rbckman/tarina/3d/tarina2.png

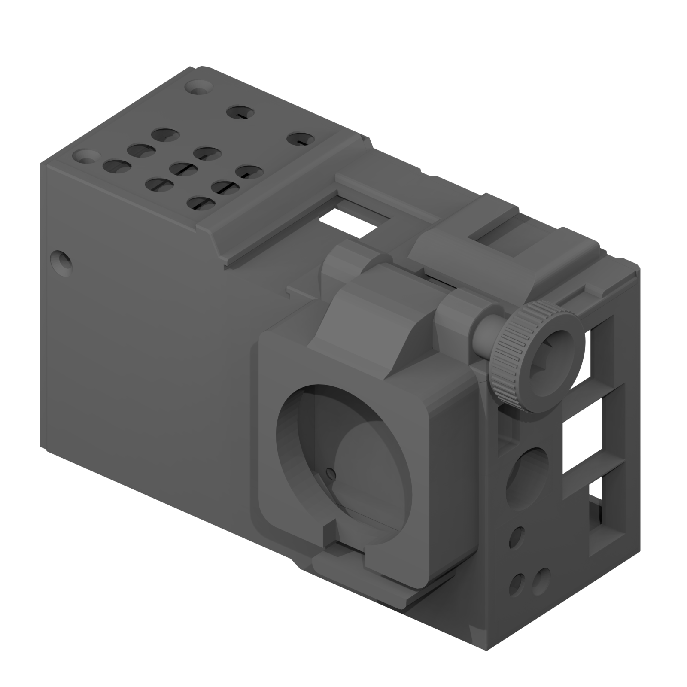
3d/tarina2.png
