rbckman/tarina/3d/tarina3.png

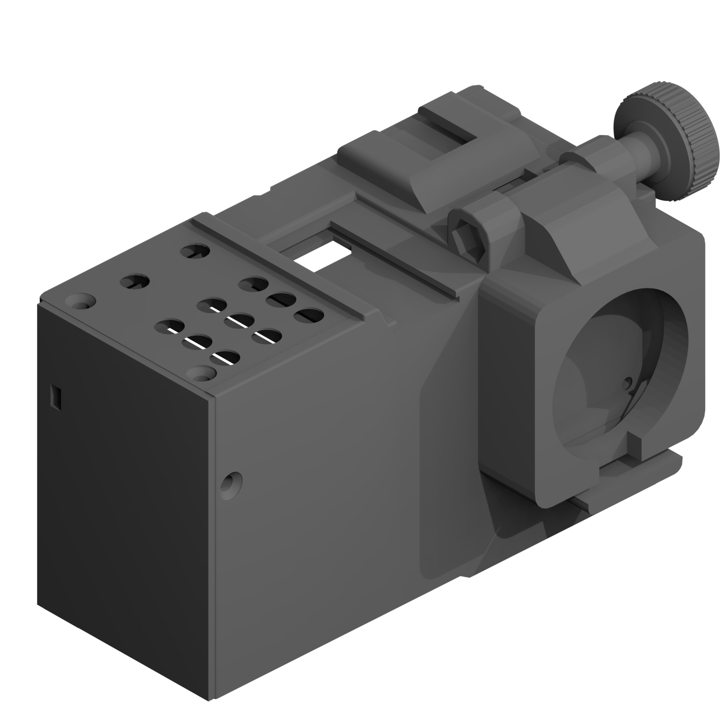
3d/tarina3.png
