rbckman/tarina/3d/tarina4.png

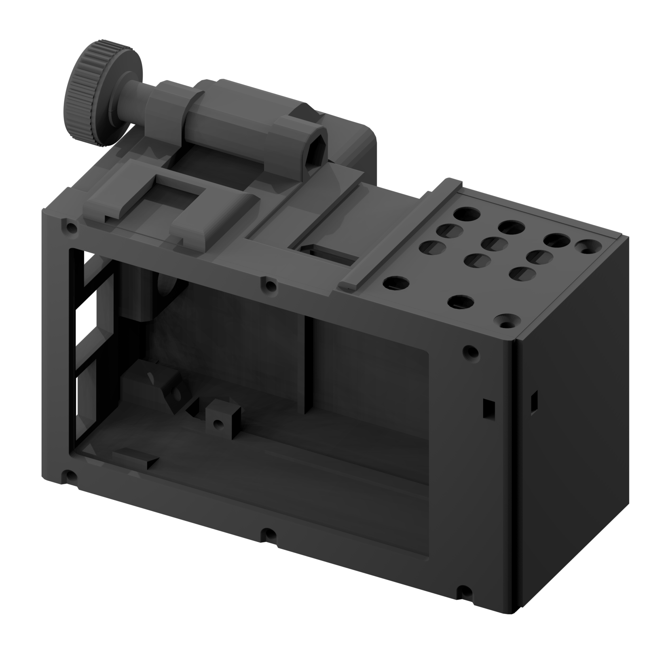
3d/tarina4.png
