rbckman/tarina/3d/tarina-body.png

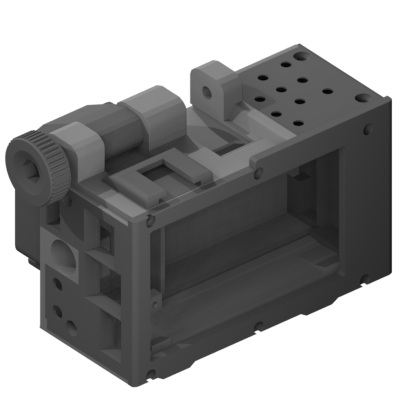
3d/tarina-body.png
