rbckman/tarina/3d/tarina-button-plate-bottom.png

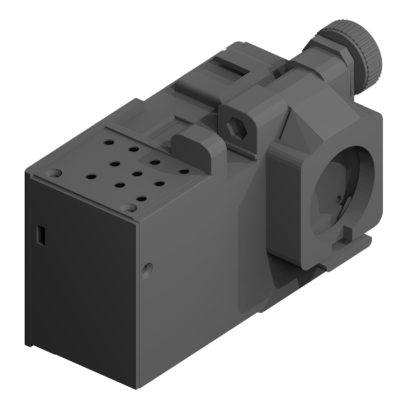
3d/tarina-button-plate-bottom.png
