rbckman/tarina/3d/tarina-button-plate-upper.png

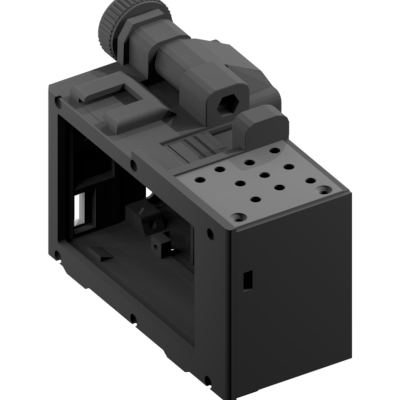
3d/tarina-button-plate-upper.png
