rbckman/tarina/3d/tarina-hdmi-cap.png

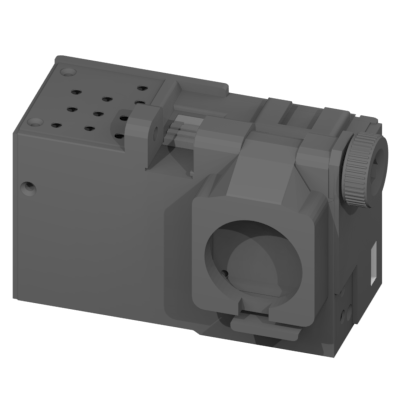
3d/tarina-hdmi-cap.png
