rbckman/tarina/3d/tarina-left-side-cap.png

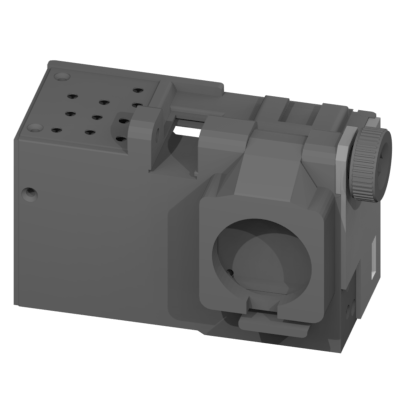
3d/tarina-left-side-cap.png
