rbckman/tarina/3d/tarina-left-side.png

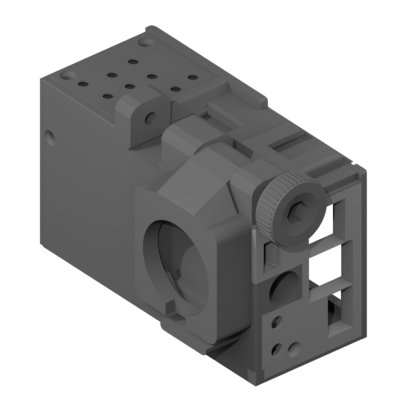
3d/tarina-left-side.png
