rbckman/tarina/3d/tarina-picamera-hq-body-lid.png

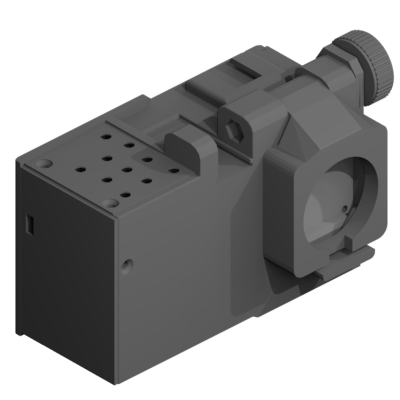
3d/tarina-picamera-hq-body-lid.png
