rbckman/tarina/3d/tarina-picamera-hq-body.png

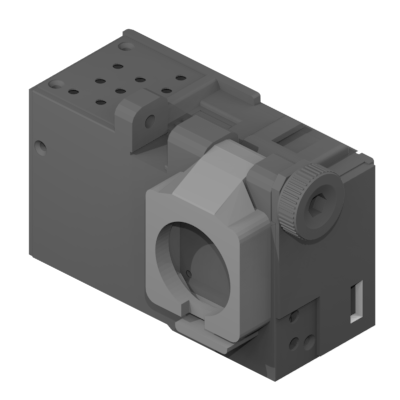
3d/tarina-picamera-hq-body.png
