rbckman/tarina/3d/tarina-picamera-screwhandle.png

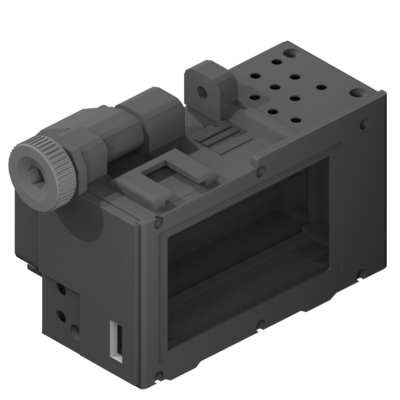
3d/tarina-picamera-screwhandle.png
