rbckman/tarina/3d/tarina-right-side.png

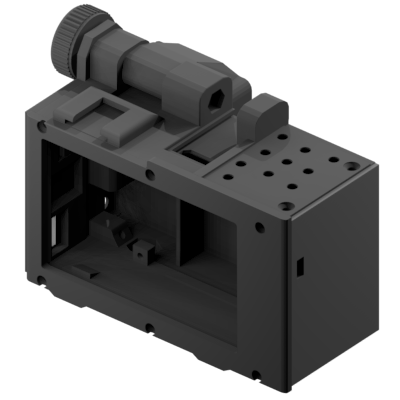
3d/tarina-right-side.png
