rbckman/tarina/3d/tarina-screen-lid-hyperpixel.png

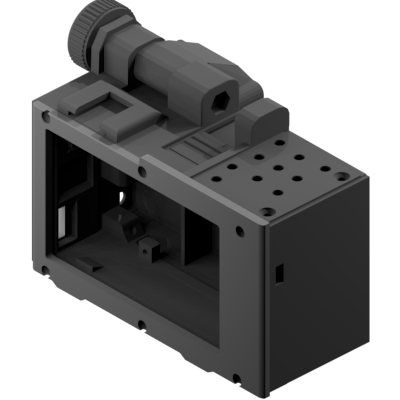
3d/tarina-screen-lid-hyperpixel.png
