rbckman/tarina/3d/tarina-screen-lid-ugeek.png

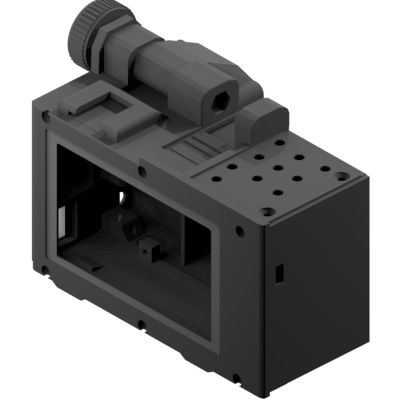
3d/tarina-screen-lid-ugeek.png
