rbckman/tarina/3d/tarina-viewfinder-hyperpixel.png

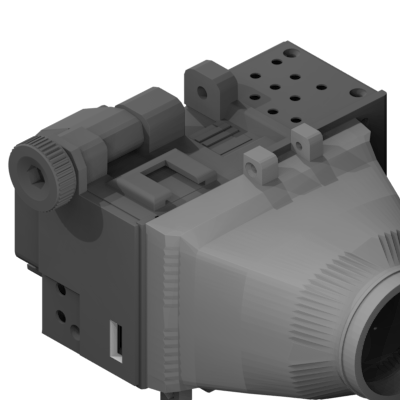
3d/tarina-viewfinder-hyperpixel.png
