rbckman/tarina/3d/tarina.png

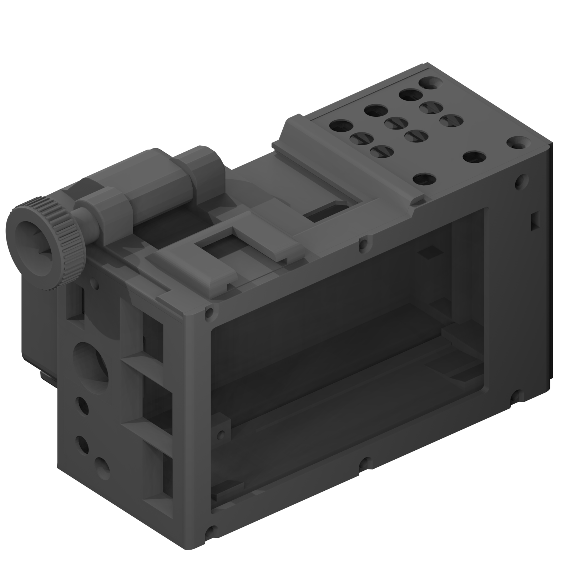
3d/tarina.png
