rbckman/tarina/docs/adafruit_powerboost1000c.png

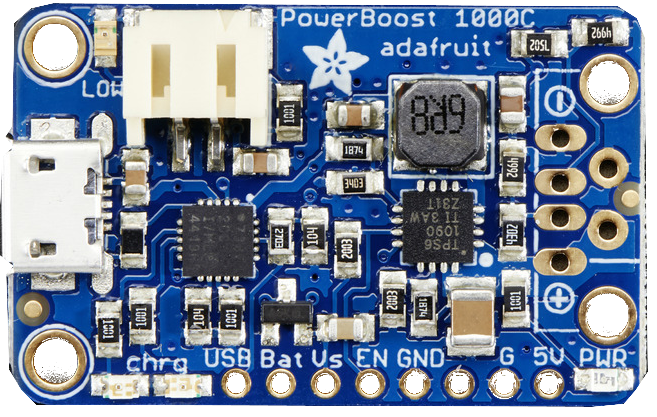
docs/adafruit_powerboost1000c.png
