rbckman/tarina/docs/hdd-cable.jpeg

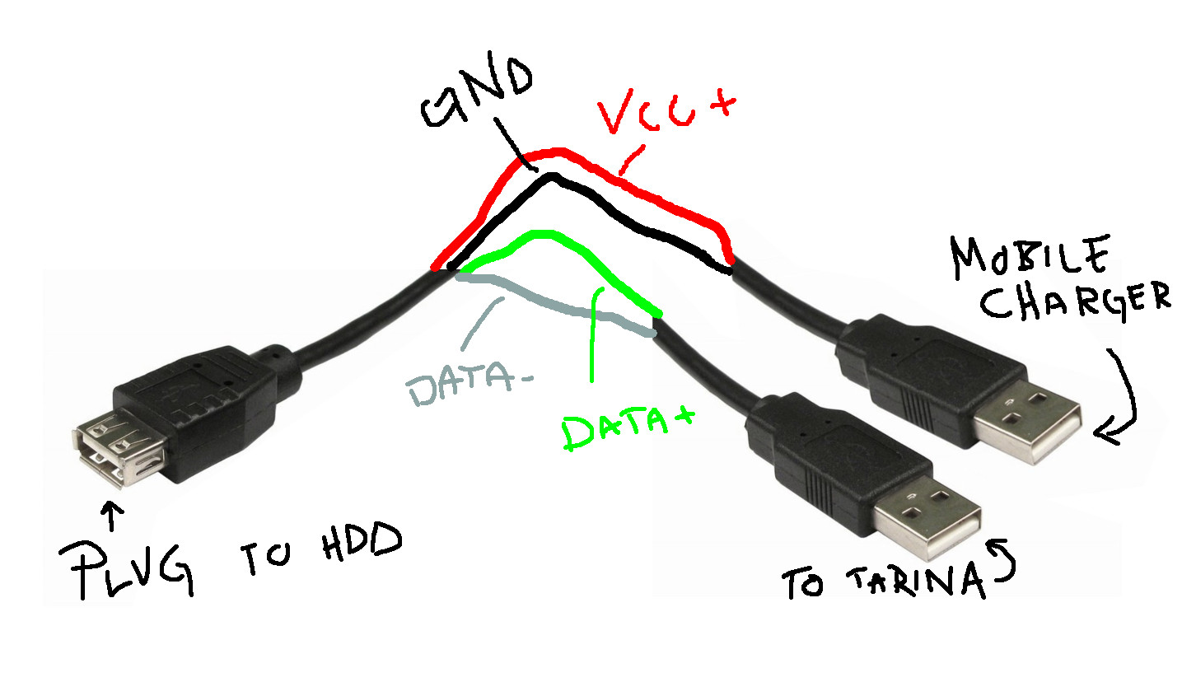
docs/hdd-cable.jpeg
