rbckman/tarina/docs/mic.png

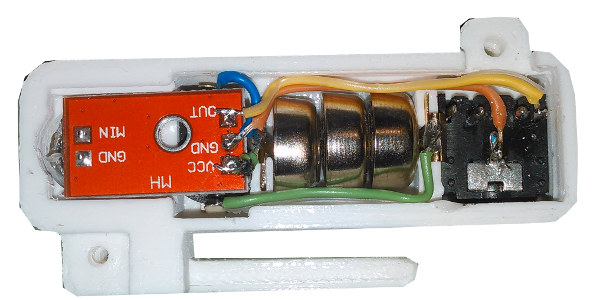
docs/mic.png
