rbckman/tarina/docs/Raspberry-Pi-3-Back.png

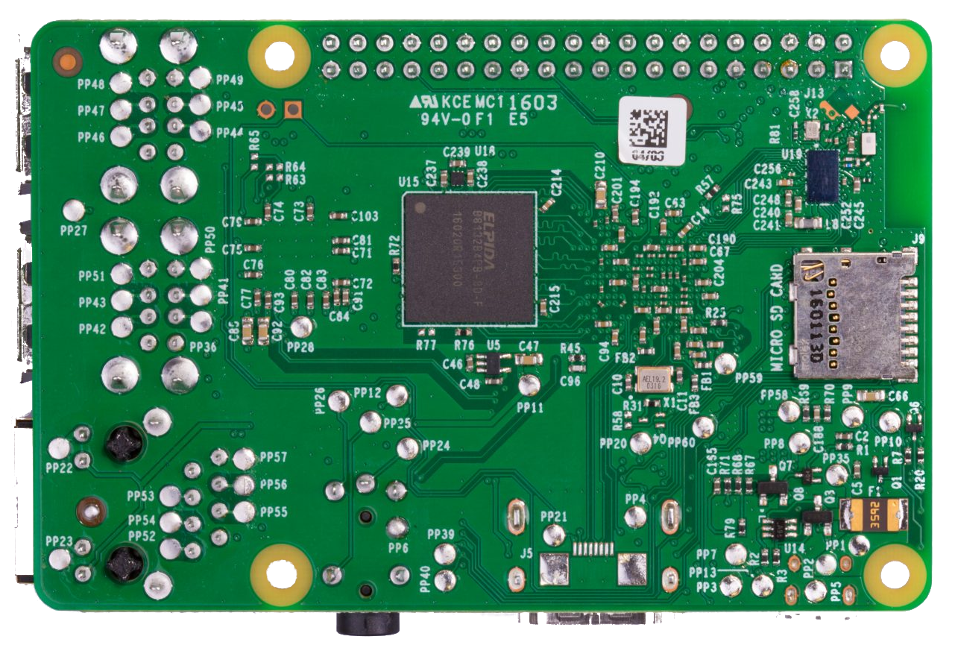
docs/Raspberry-Pi-3-Back.png
