rbckman/tarina/docs/soundcard.png

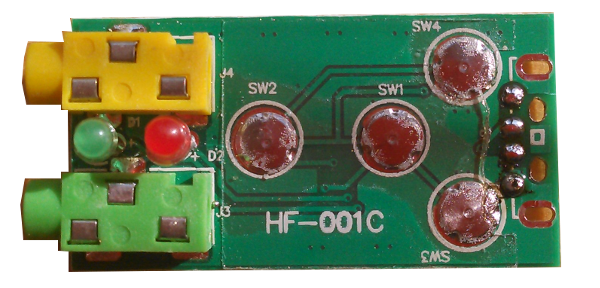
docs/soundcard.png
