rbckman/tarina/docs/tarina-and-leon.jpg

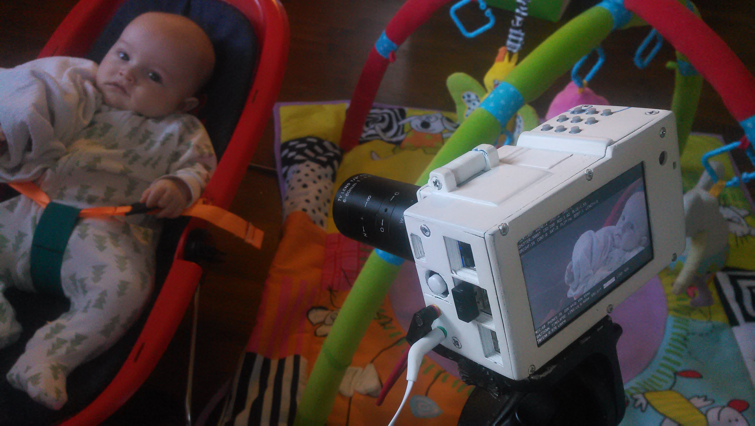
docs/tarina-and-leon.jpg
