rbckman/tarina/docs/tarina-mob.jpg

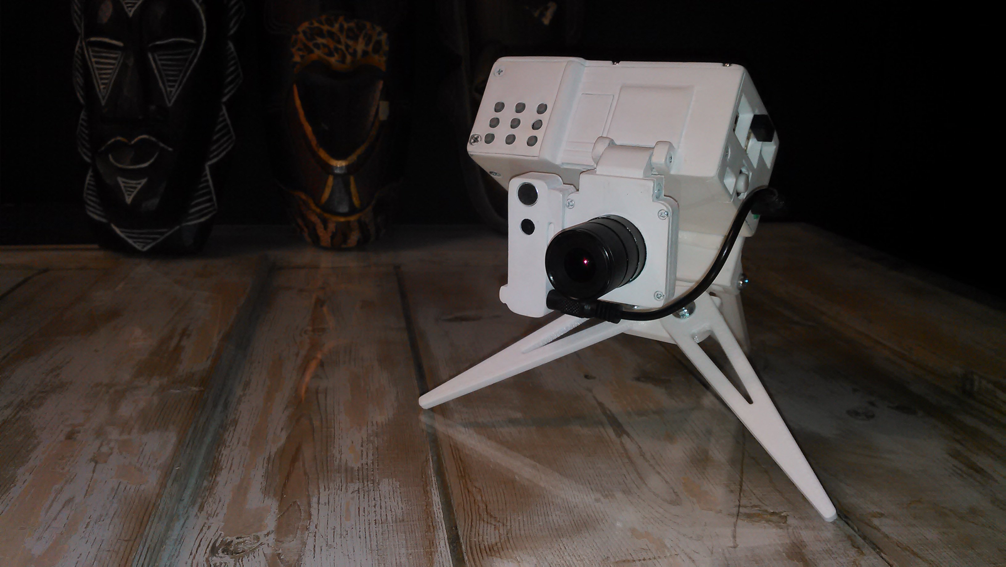
docs/tarina-mob.jpg
