rbckman/tarina/extras/buttons.png

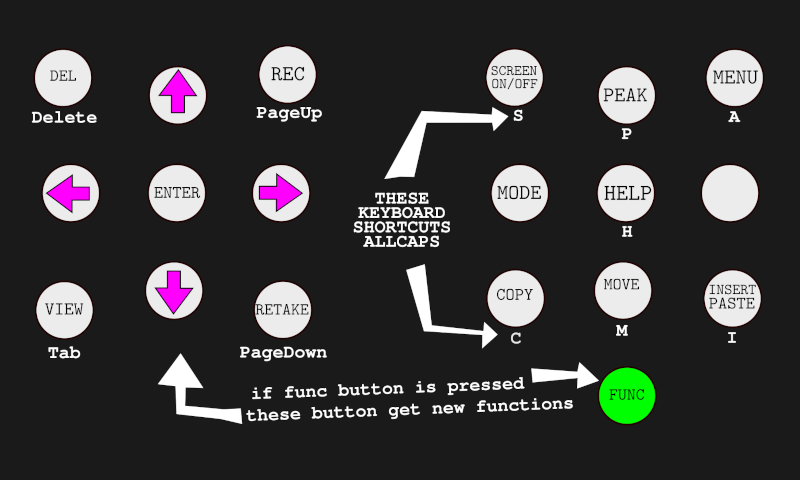
extras/buttons.png
