rbckman/tarina/3d/tarina-right-side.stl

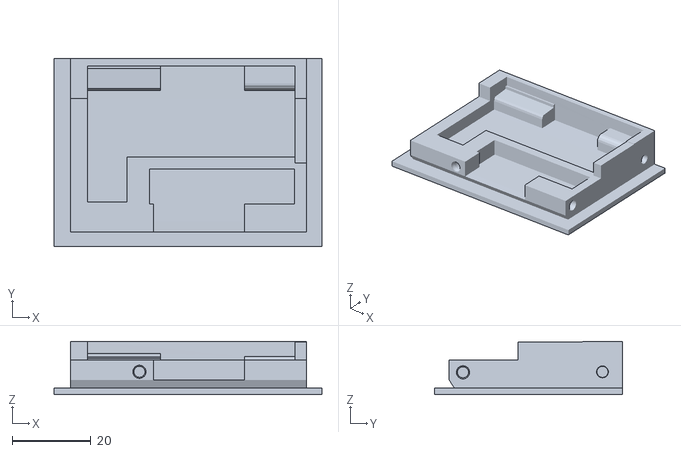
[picture p43: CAD file, 2023-09-10]
3d/tarina-right-side.stl
67.9 x 47.6 x 13.5
