rbckman/tarina/3d/tarina-screen-lid-ugeek.stl

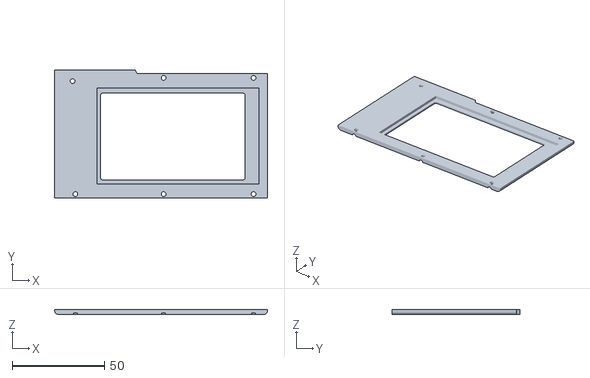
[picture p44: CAD file, 2023-09-02]
3d/tarina-screen-lid-ugeek.stl
115.7 x 69.6 x 2.70
