rbckman/tarina/3d/tarina-picamera-hq-body-lid.stl

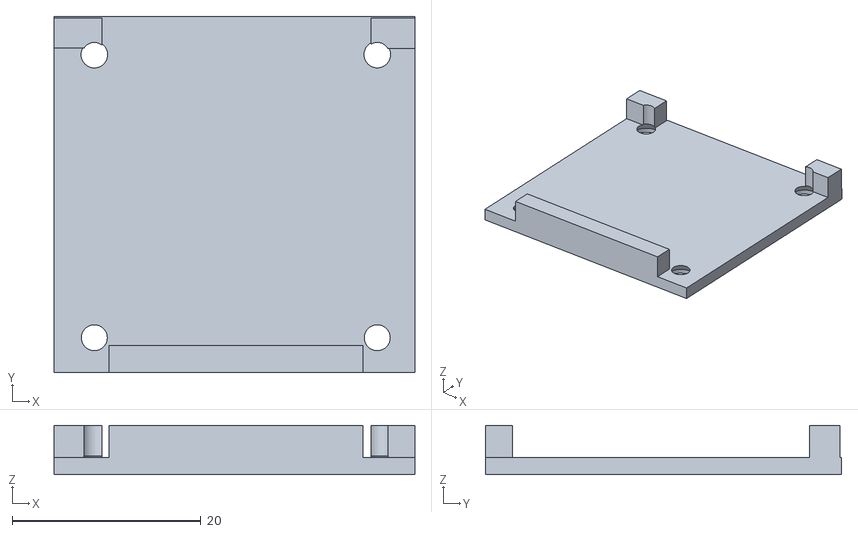
[picture p45: CAD file, 2023-09-02]
3d/tarina-picamera-hq-body-lid.stl
38.2 x 37.7 x 5.24
