rbckman/tarina/3d/viewfinder-clip-bridge3.stl

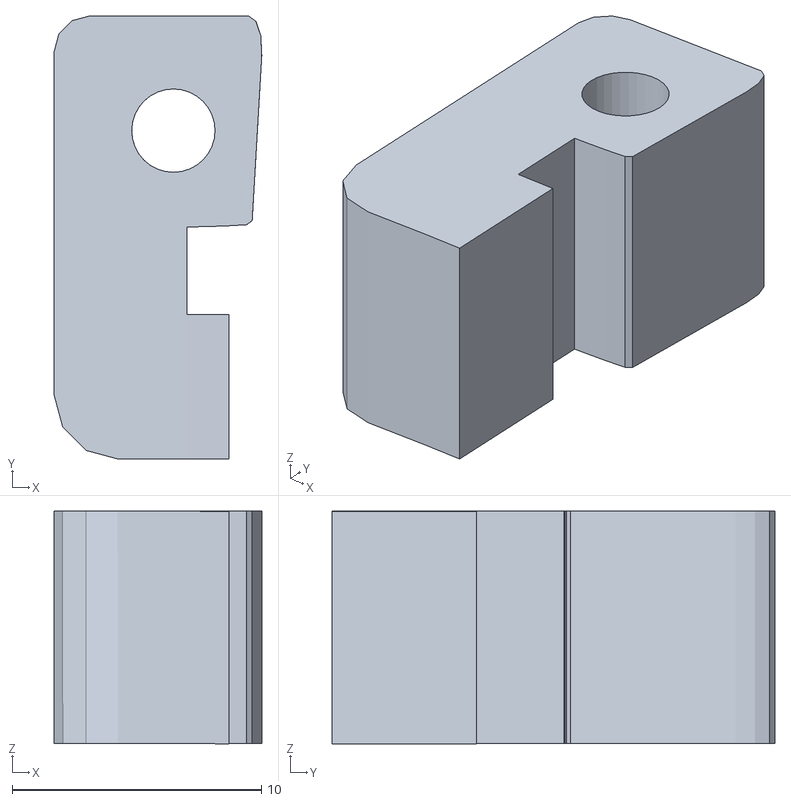
[picture p46: CAD file, 2023-08-19]
3d/viewfinder-clip-bridge3.stl
8.32 x 17.8 x 9.33
