rbckman/tarina/3d/tarina-modifyer-body-logo.stl

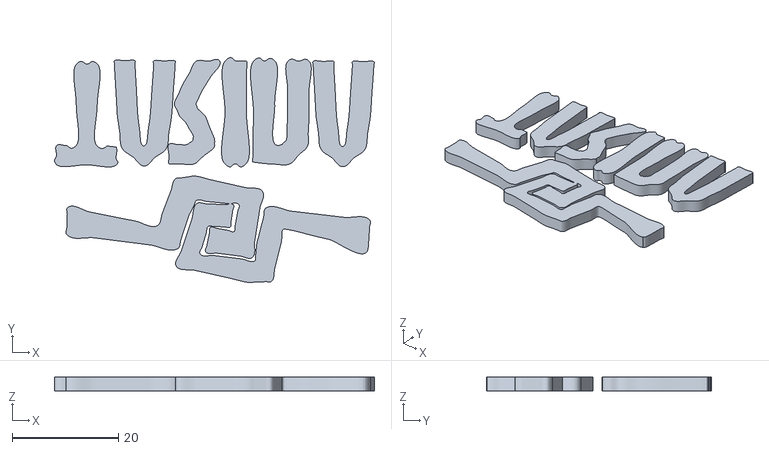
[picture p47: CAD file, 2023-08-19]
3d/tarina-modifyer-body-logo.stl
60.2 x 42.3 x 2.57
