rbckman/tarina/3d/tarina-modifyer-button-icons.stl

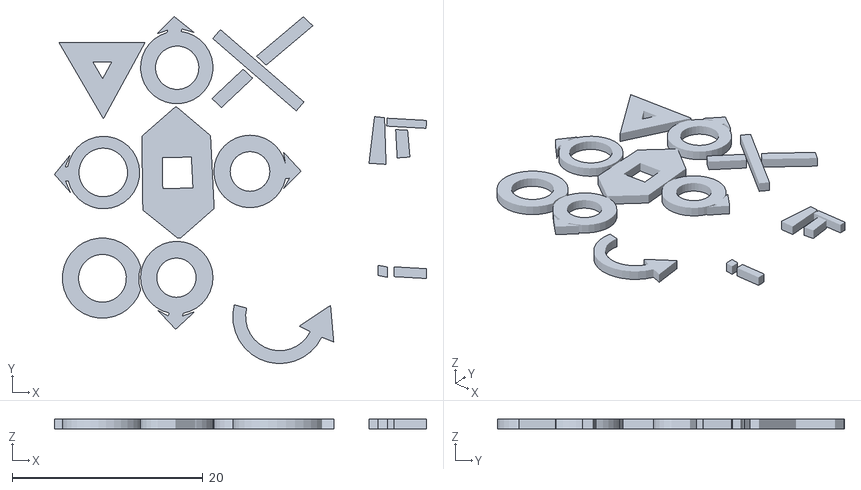
[picture p48: CAD file, 2023-08-19]
3d/tarina-modifyer-button-icons.stl
39.0 x 36.4 x 1.10
