rbckman/tarina/3d/viewfinder-clip-bridge2.stl

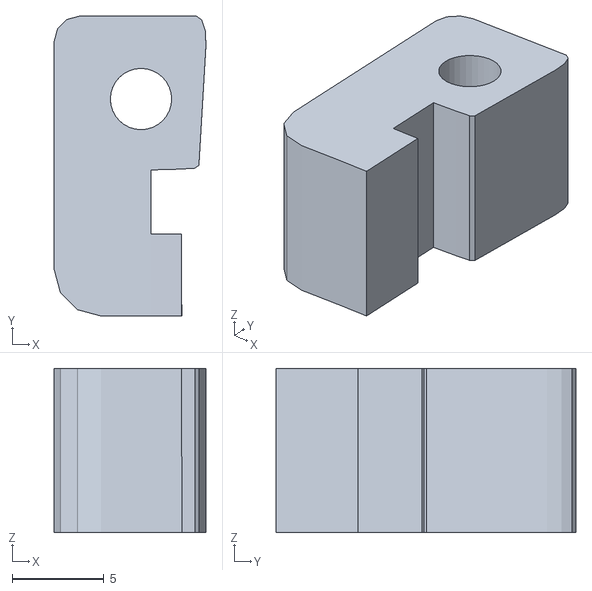
[picture p49: CAD file, 2023-08-19]
3d/viewfinder-clip-bridge2.stl
8.29 x 16.4 x 8.96
