rbckman/tarina/3d/tarina-viewfinder-hyperpixel.stl

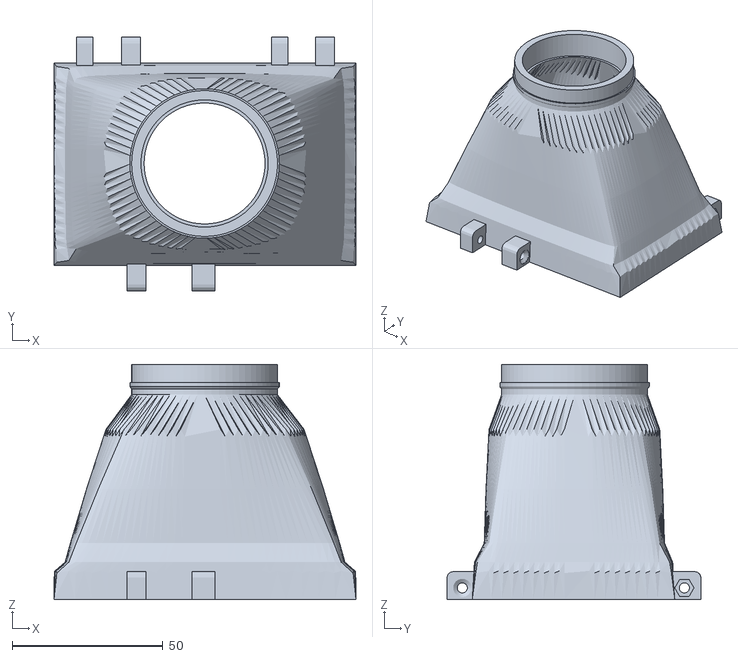
[picture p50: CAD file, 2023-08-19]
3d/tarina-viewfinder-hyperpixel.stl
100.2 x 84.3 x 78.0
