rbckman/tarina/3d/tarina-viewfinder-eyepiece.stl

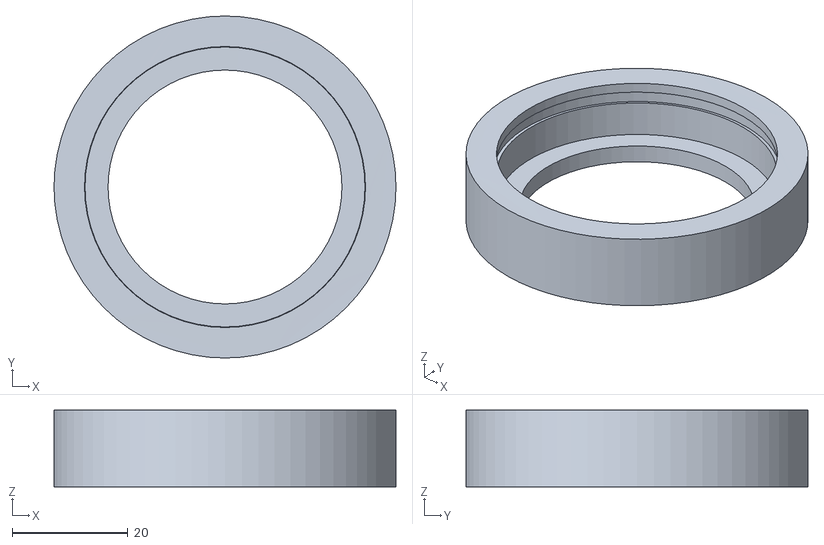
[picture p51: CAD file, 2023-08-19]
3d/tarina-viewfinder-eyepiece.stl
59.1 x 59.1 x 13.3
