rbckman/tarina/3d/viewfinder-clip-bridge.stl

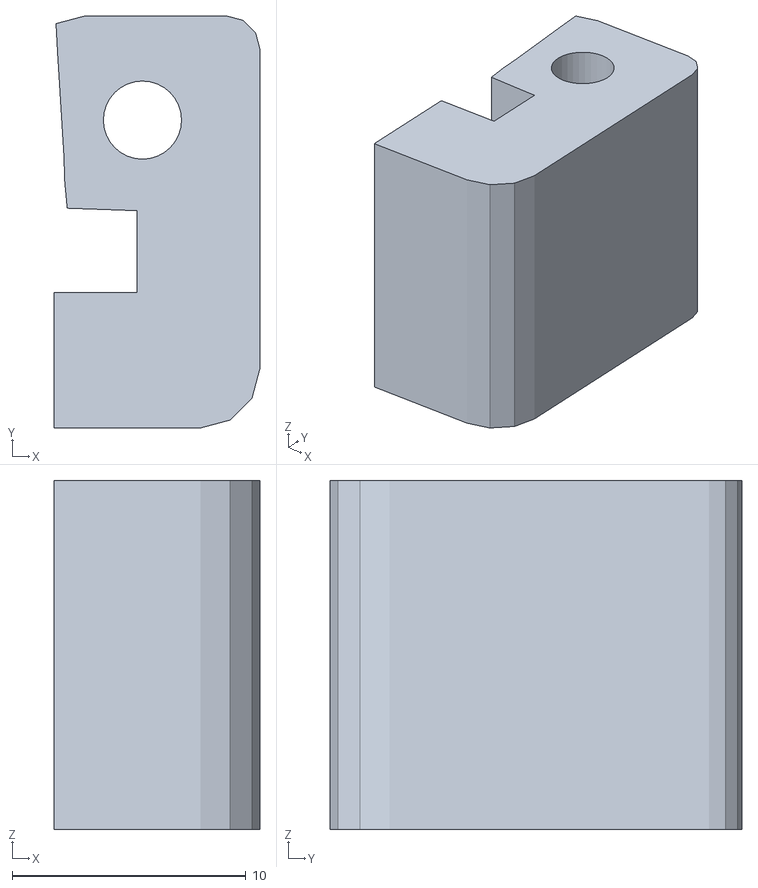
[picture p52: CAD file, 2023-08-19]
3d/viewfinder-clip-bridge.stl
8.80 x 17.6 x 14.9
