rbckman/tarina/3d/tarina-picamera-body.stl

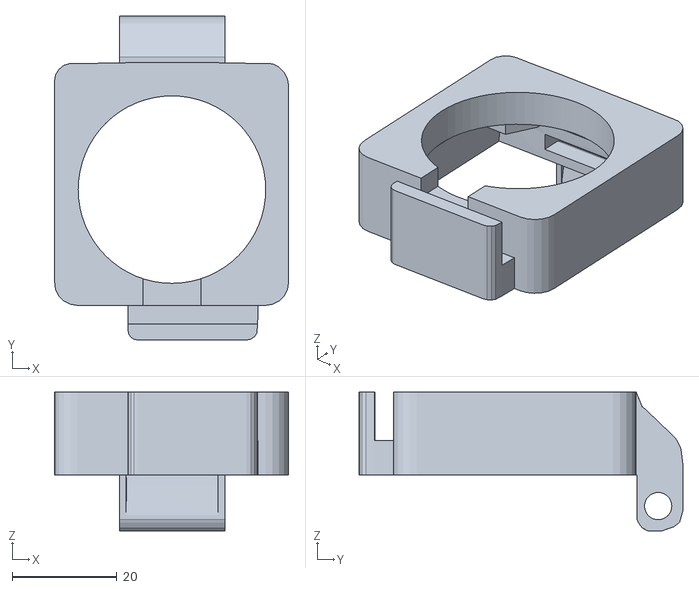
[picture p53: CAD file, 2022-04-14]
3d/tarina-picamera-body.stl
44.7 x 61.9 x 26.5
