rbckman/tarina/3d/tarina-picamera-body-lid.stl

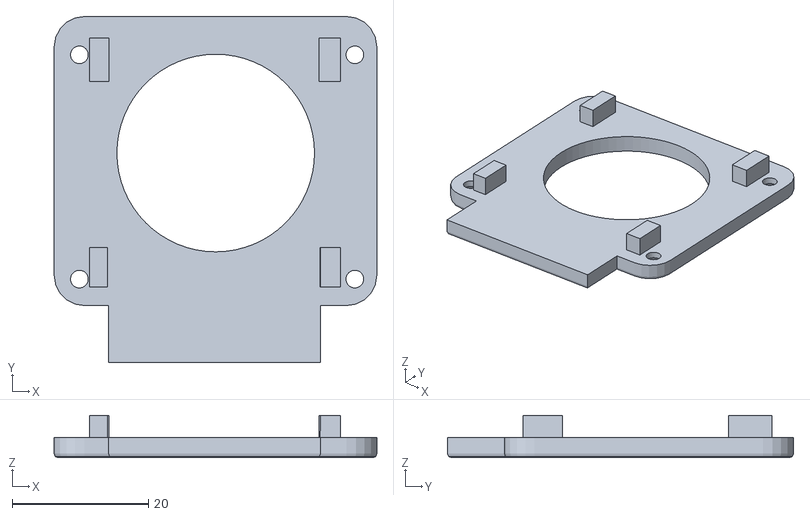
[picture p54: CAD file, 2022-01-14]
3d/tarina-picamera-body-lid.stl
47.4 x 50.8 x 6.22
