rbckman/tarina/3d/tarina-picamera-bridge.stl

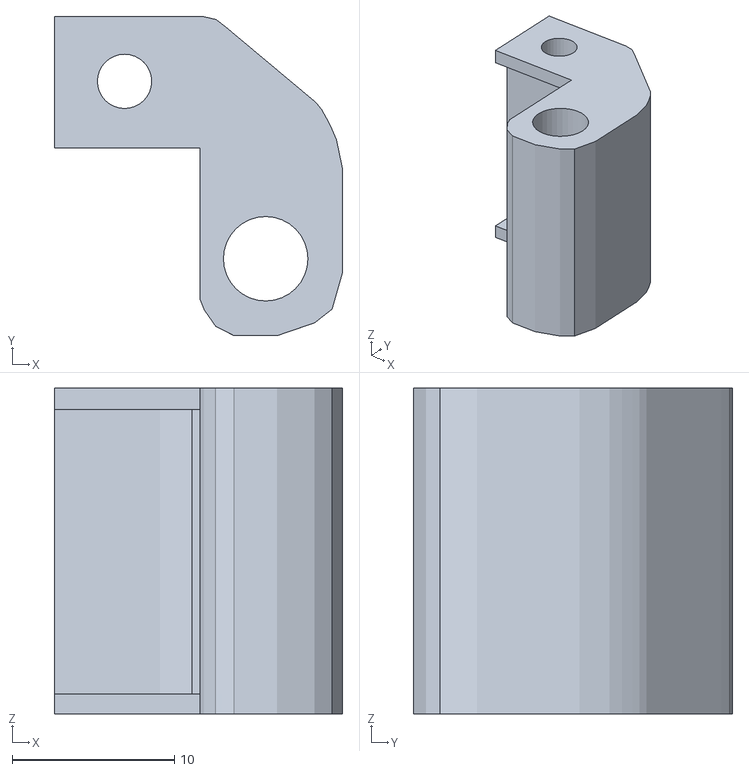
[picture p55: CAD file, 2022-01-14]
3d/tarina-picamera-bridge.stl
17.8 x 19.7 x 20.1
