rbckman/tarina/3d/tarina-screen-lid.stl

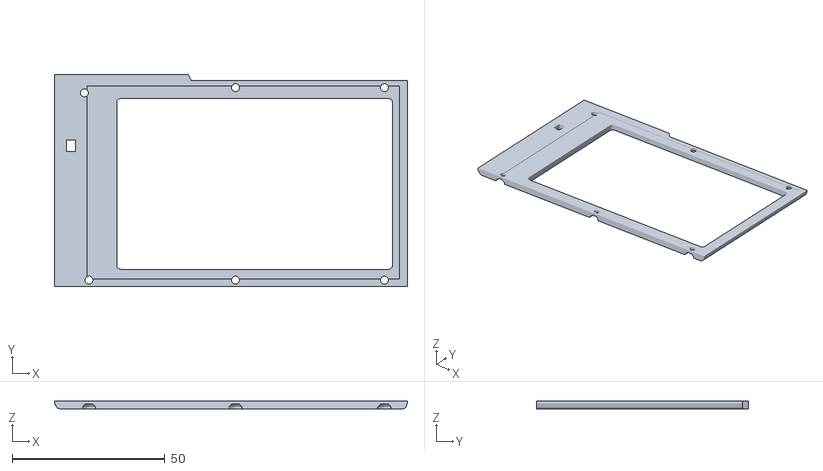
[picture p56: CAD file, 2021-04-11]
3d/tarina-screen-lid.stl
115.7 x 69.6 x 2.70
