rbckman/tarina/3d/tarina-viewfinder.stl

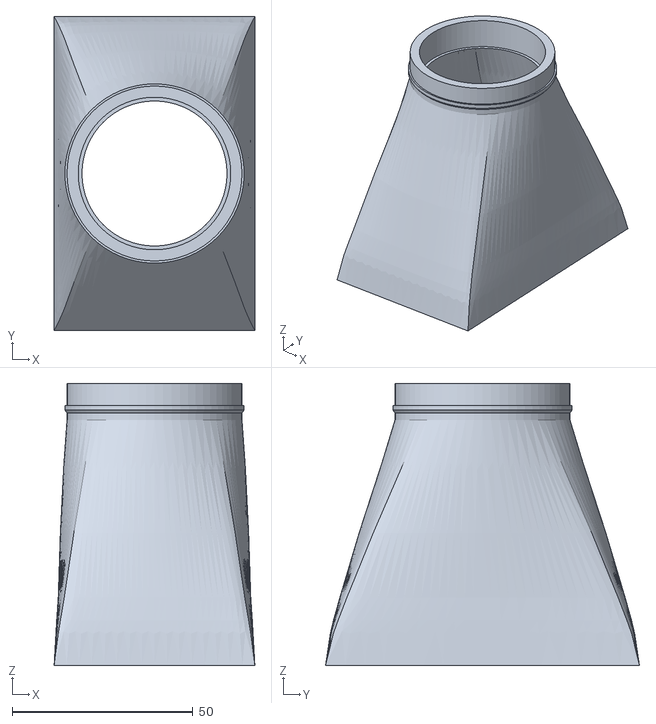
[picture p57: CAD file, 2020-01-06]
3d/tarina-viewfinder.stl
55.6 x 86.9 x 78.0
