rbckman/tarina/3d/tarina-plate.stl

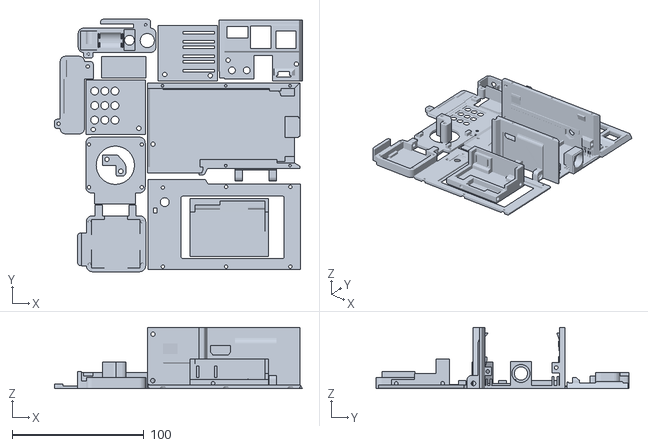
[picture p58: CAD file, 2019-12-02]
3d/tarina-plate.stl
188.3 x 191.7 x 46.5
