rbckman/tarina/docs/tarina-build-06.jpg

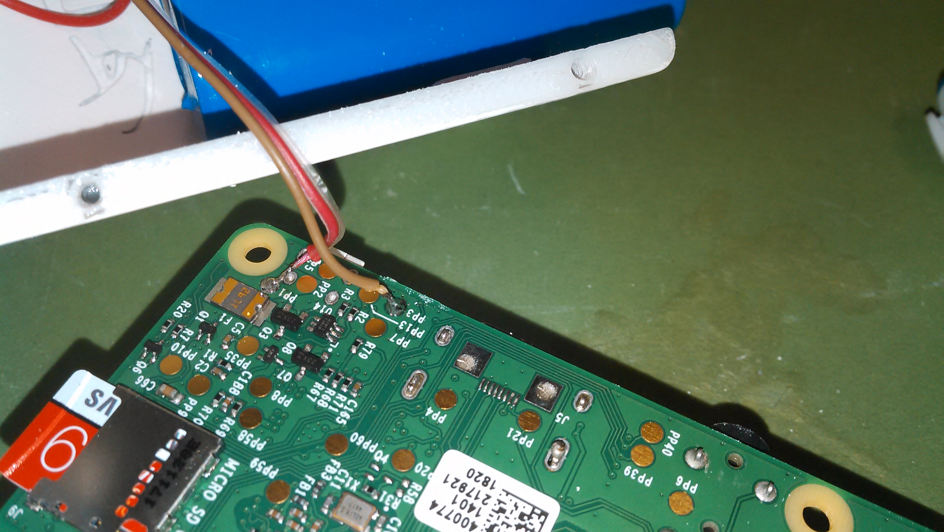
docs/tarina-build-06.jpg
