rbckman/tarina/docs/tarina-build-09.jpg

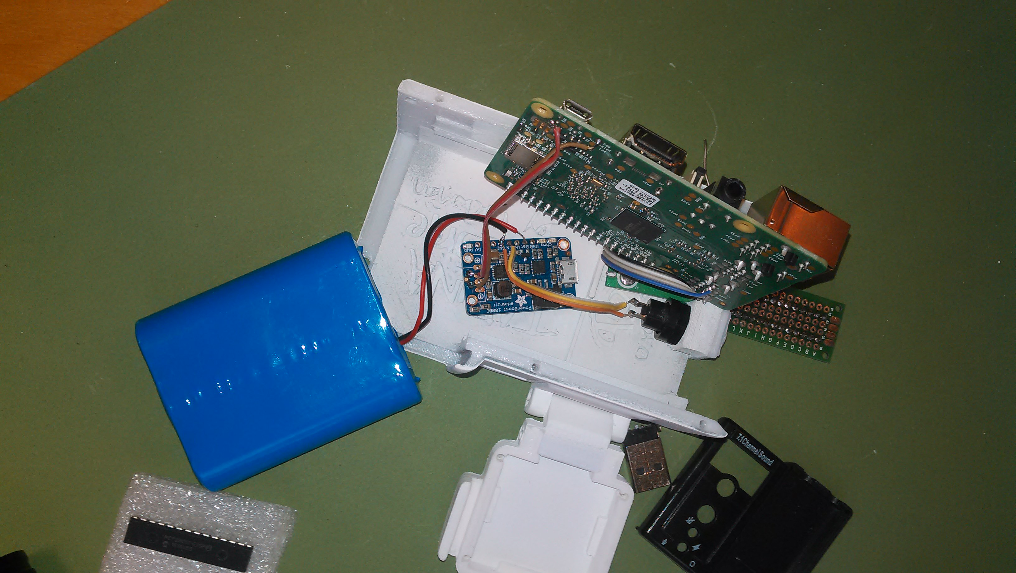
docs/tarina-build-09.jpg
