rbckman/tarina/docs/tarina-build-12.jpg

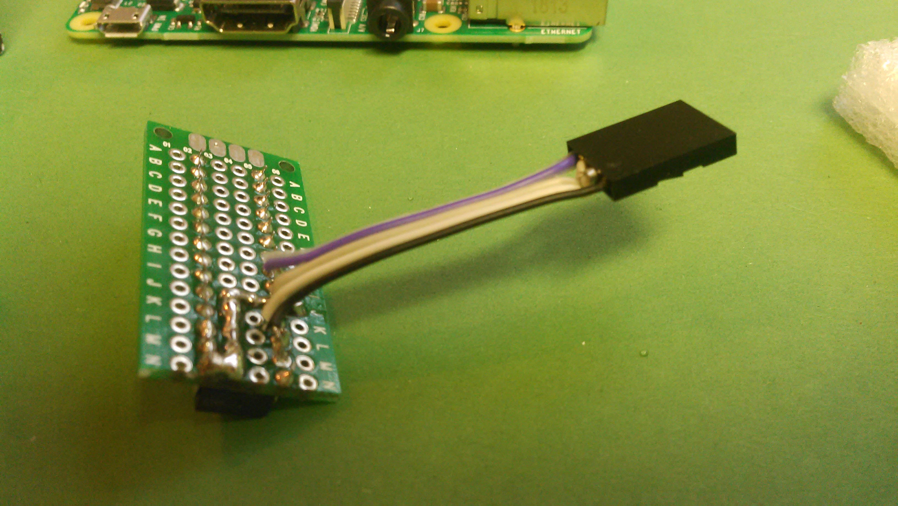
docs/tarina-build-12.jpg
